isarachol/EC535_FINAL_PROJECT/CAD/two-legged-v1/Part Studio 1 - riser.stl

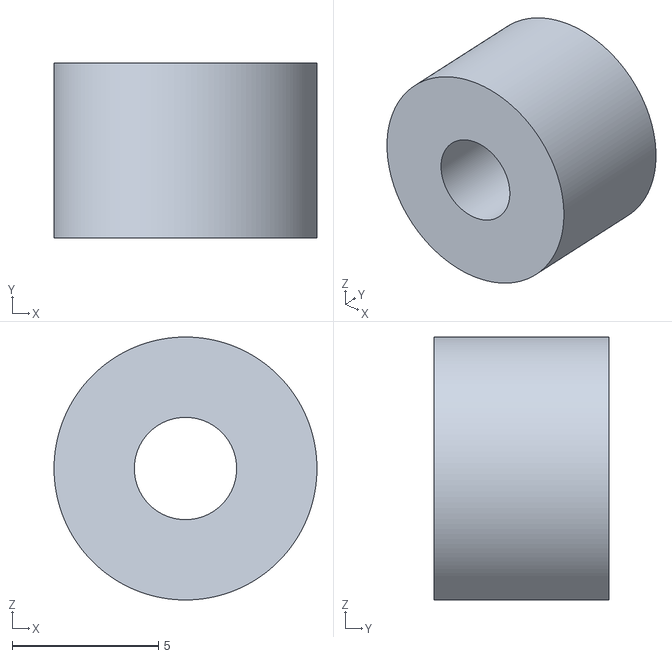
[picture p17: CAD file, 2025-12-01]
CAD/two-legged-v1/Part Studio 1 - riser.stl
9.00 x 6.00 x 9.00
